RivasMario/SKYWAY-96/Case/96% Case (RobotDoctor)/Images/96plate_angle_left.png

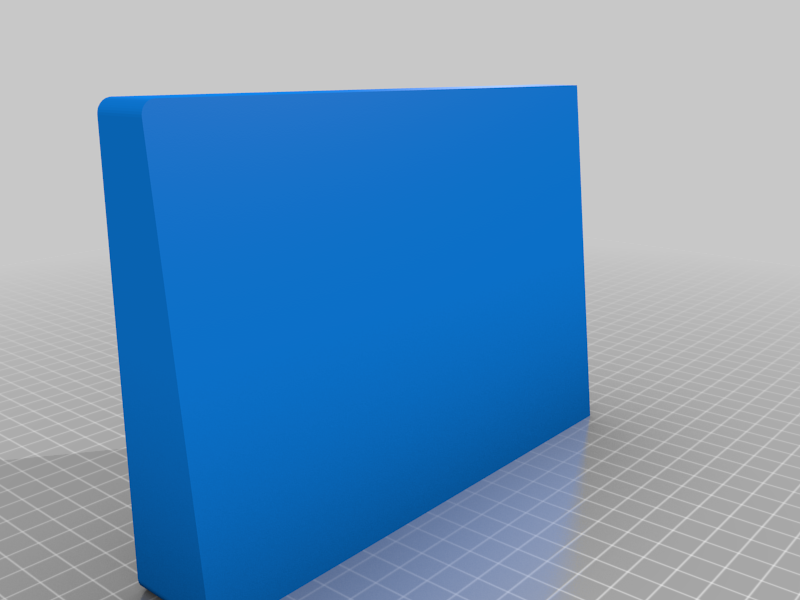
Case/96% Case (RobotDoctor)/Images/96plate_angle_left.png
