RivasMario/SKYWAY-96/Case/SKYWAY Custom (CadQuery)/output/foot_dovetail.png

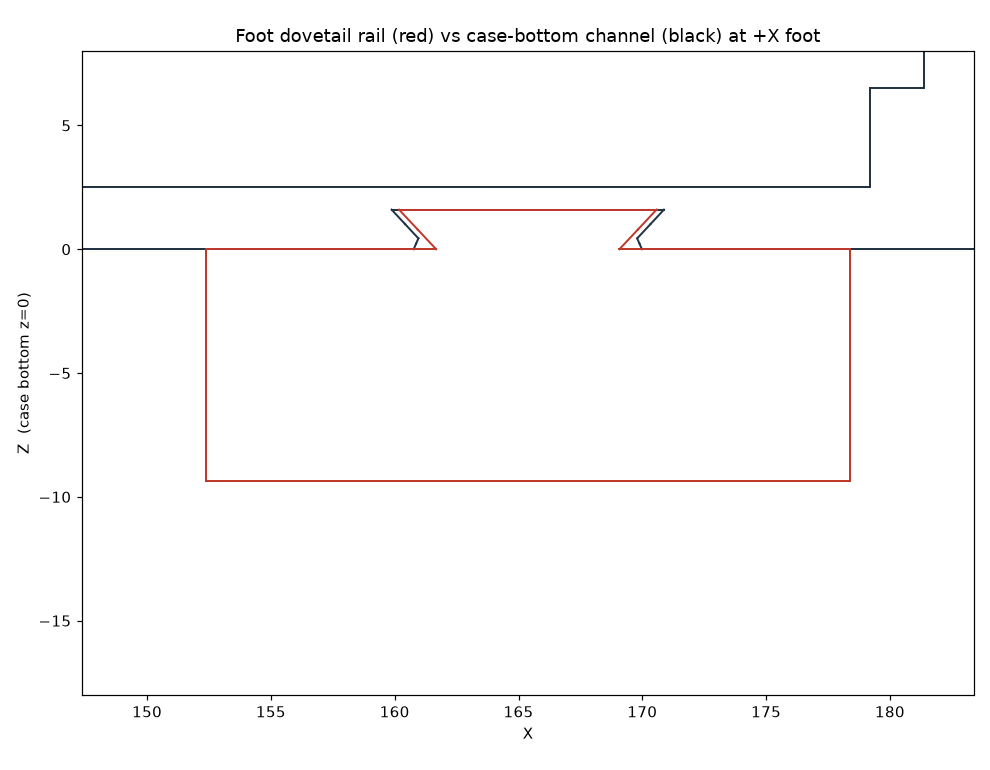
Case/SKYWAY Custom (CadQuery)/output/foot_dovetail.png
