RivasMario/SKYWAY-96/Case/SKYWAY Custom (CadQuery)/output/orientation_check.png

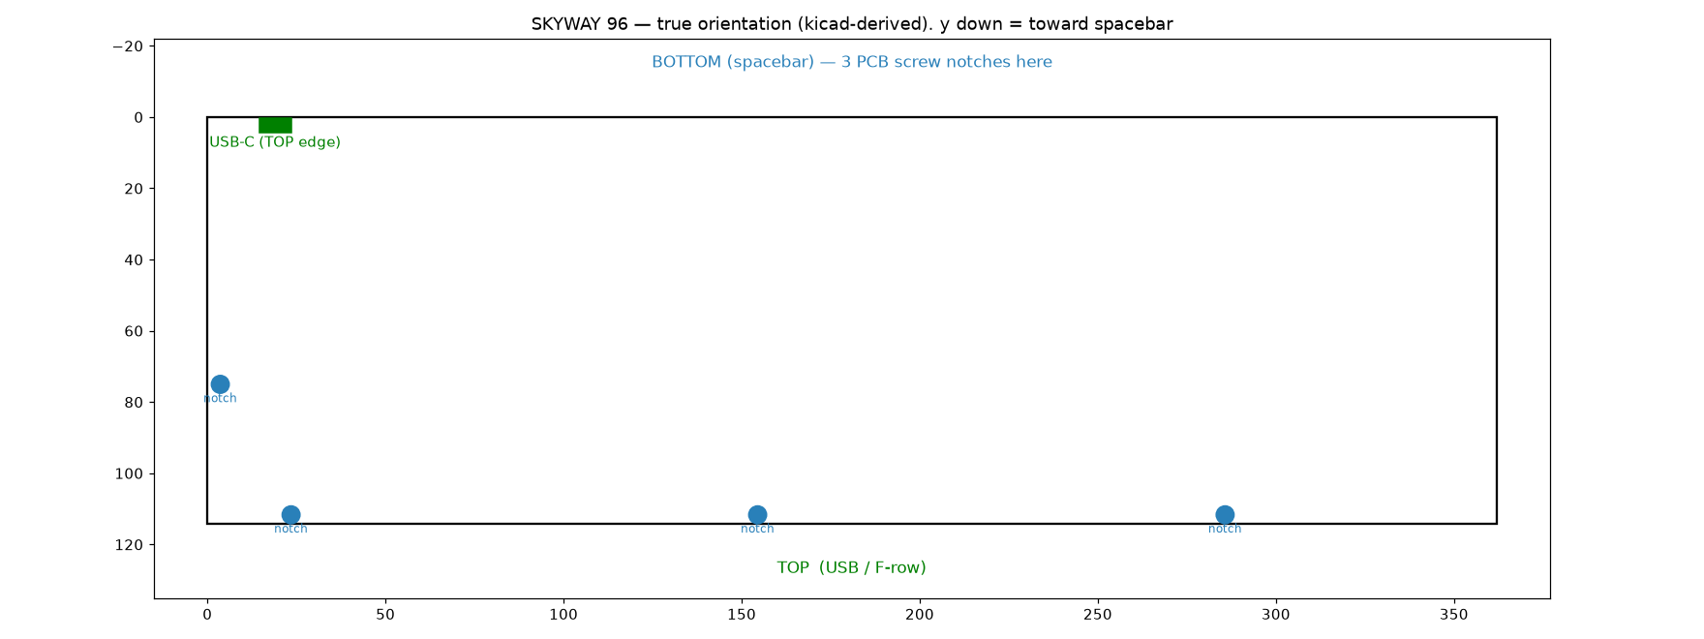
Case/SKYWAY Custom (CadQuery)/output/orientation_check.png
