RivasMario/SKYWAY-96/Case/SKYWAY Custom (CadQuery)/output/overhang_map.png

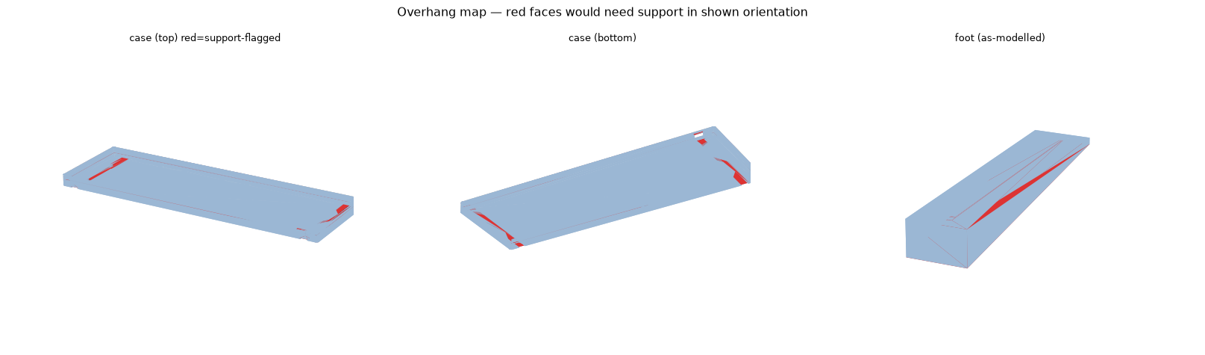
Case/SKYWAY Custom (CadQuery)/output/overhang_map.png
