RivasMario/SKYWAY-96/Case/SKYWAY Custom (CadQuery)/output/posts_topcheck.png

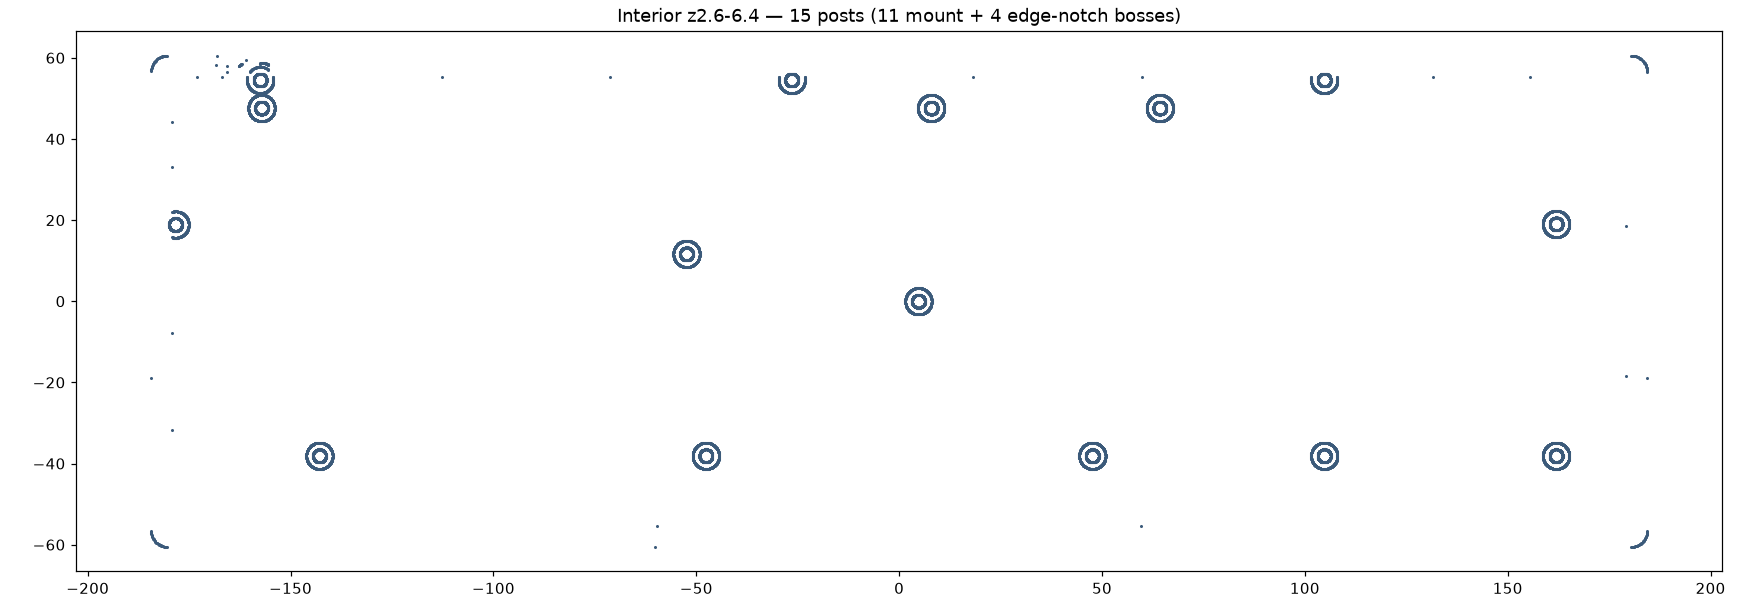
Case/SKYWAY Custom (CadQuery)/output/posts_topcheck.png
