RivasMario/SKYWAY-96/Case/SKYWAY Custom (CadQuery)/output/screw_map.png

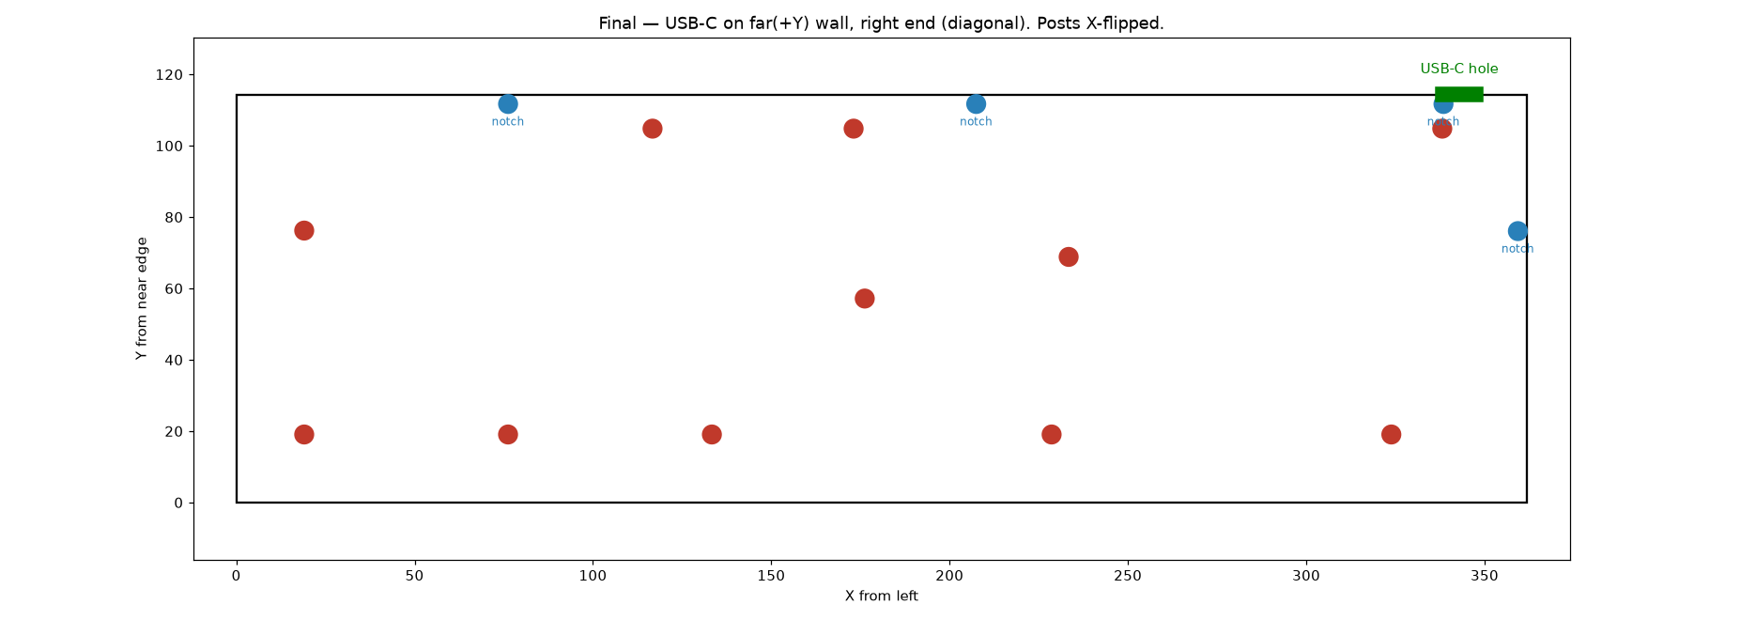
Case/SKYWAY Custom (CadQuery)/output/screw_map.png
