RivasMario/SKYWAY-96/Case/SKYWAY Custom (CadQuery)/output/split_dovetail.png

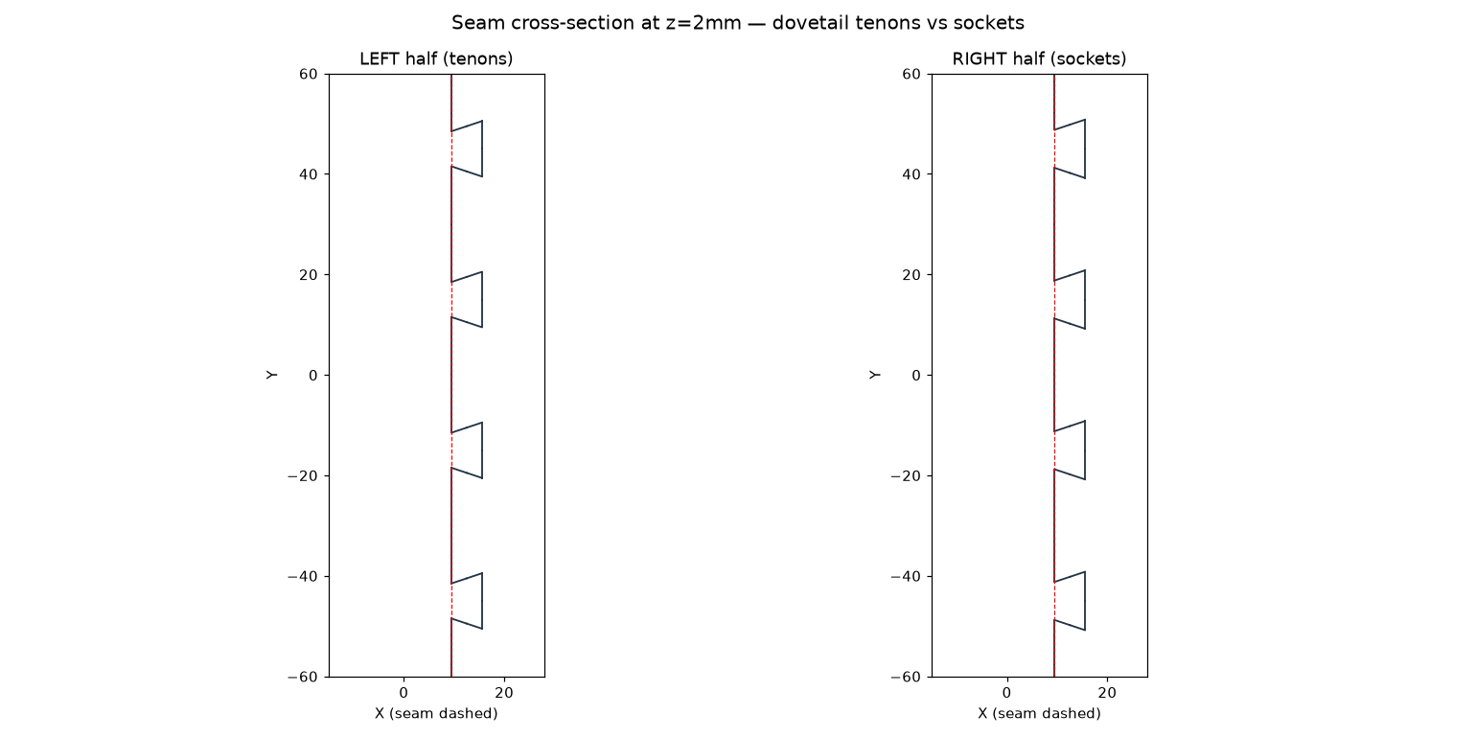
Case/SKYWAY Custom (CadQuery)/output/split_dovetail.png
