RivasMario/SKYWAY-96/Case/SKYWAY Custom (CadQuery)/output/variants_preview.png

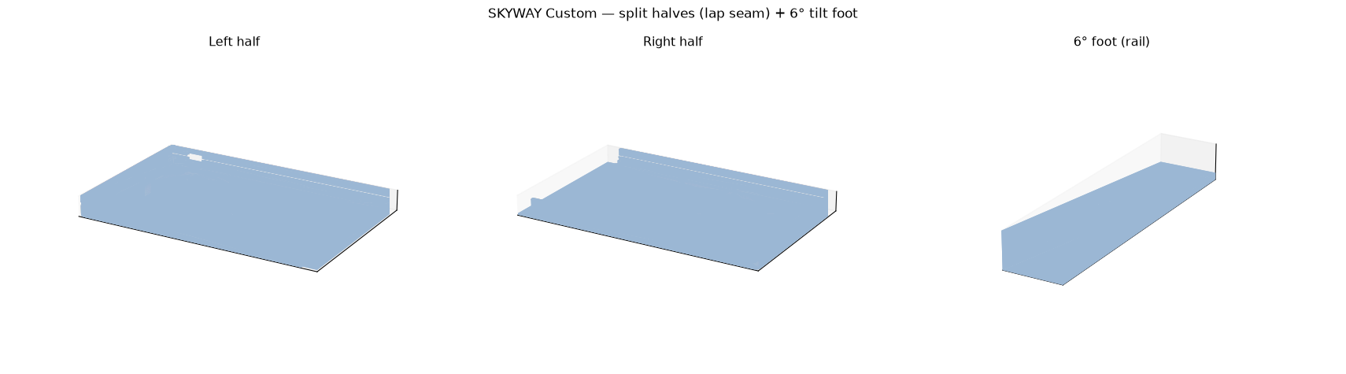
Case/SKYWAY Custom (CadQuery)/output/variants_preview.png
