RivasMario/SKYWAY-96/KLE DATA/Keys.png

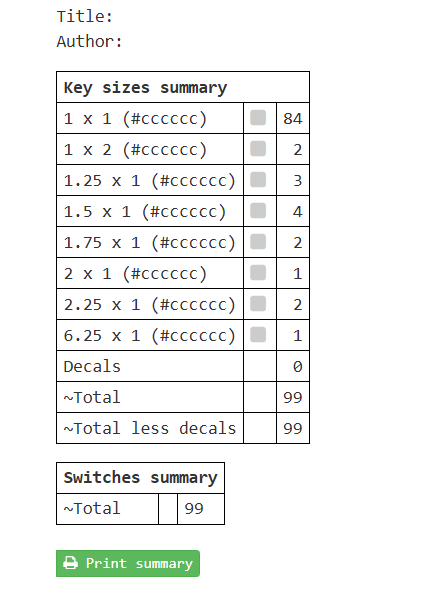
KLE DATA/Keys.png
