RivasMario/SKYWAY-96/KLE DATA/Via Labelling.png

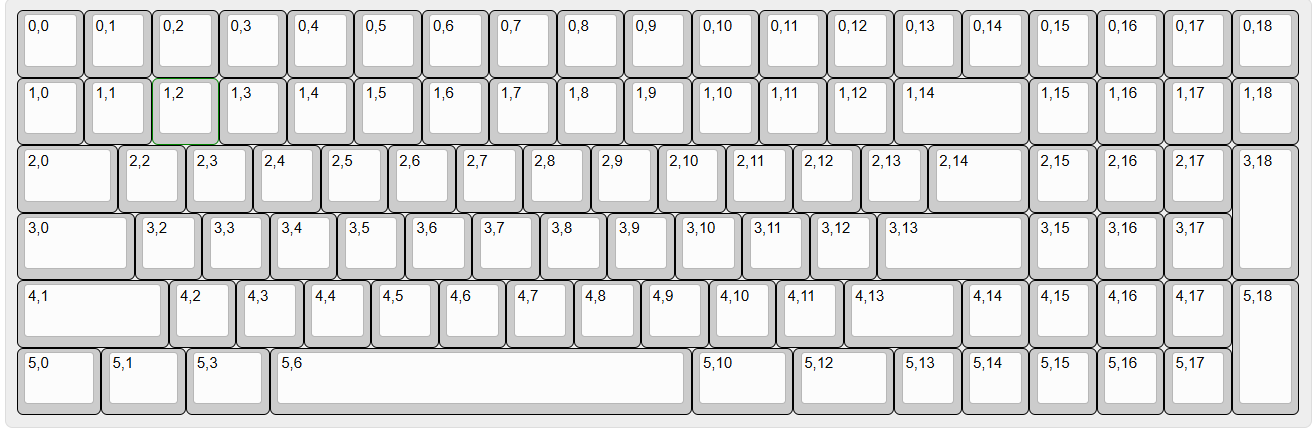
KLE DATA/Via Labelling.png
