RivasMario/SKYWAY-96/Photos/3D.webp

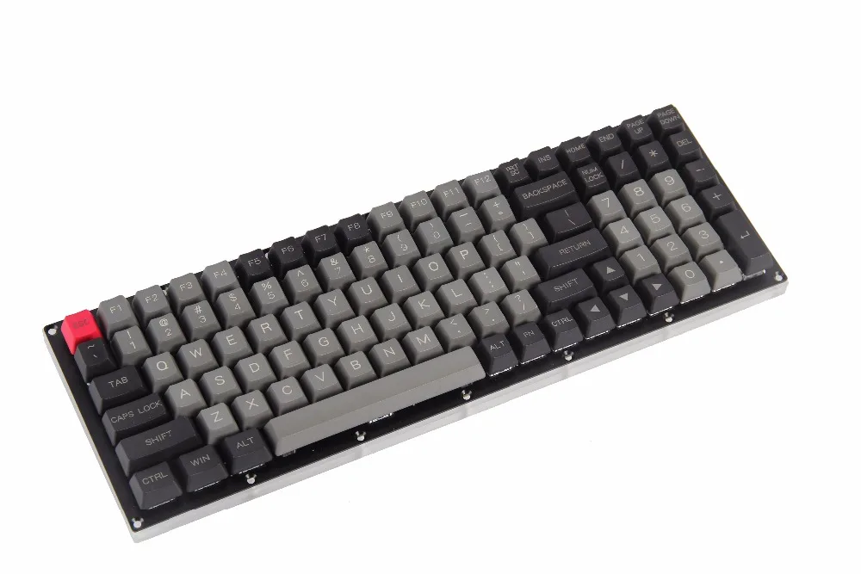
Photos/3D.webp
