RivasMario/SKYWAY-96/Photos/PCB.png

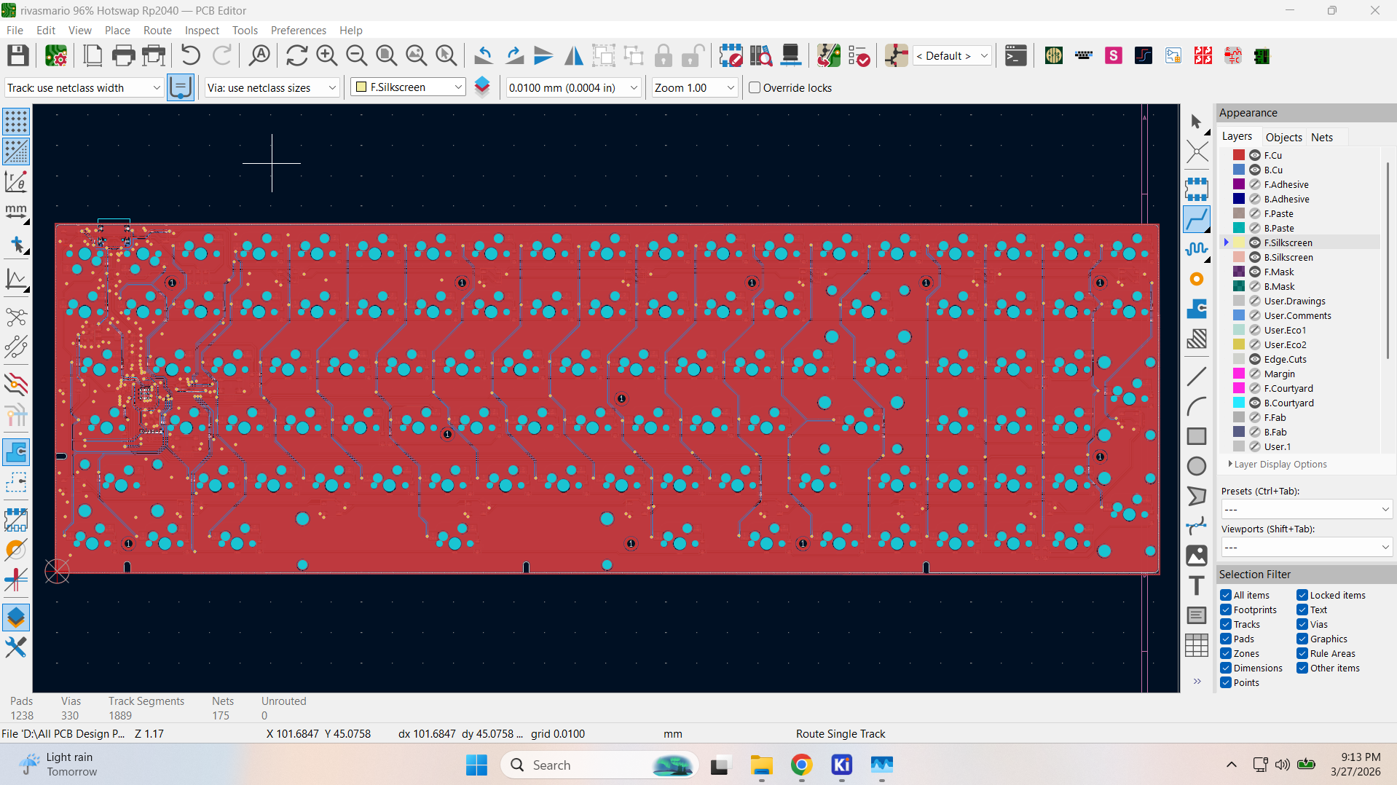
Photos/PCB.png
