RivasMario/SKYWAY-96/Photos/Stablizers.png

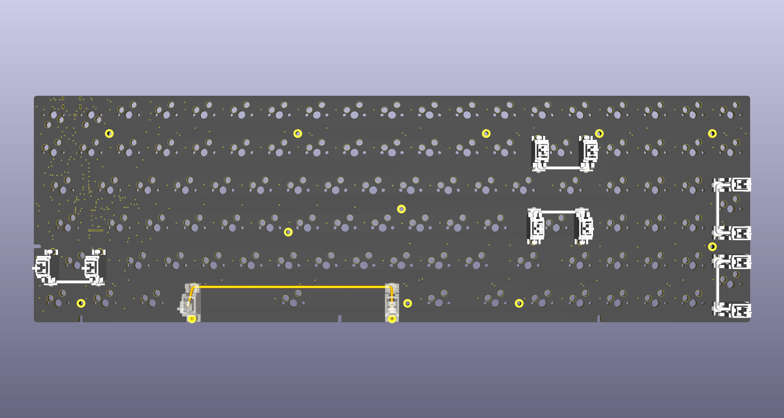
Photos/Stablizers.png
