RivasMario/SKYWAY-96/Photos/Top 2D.png

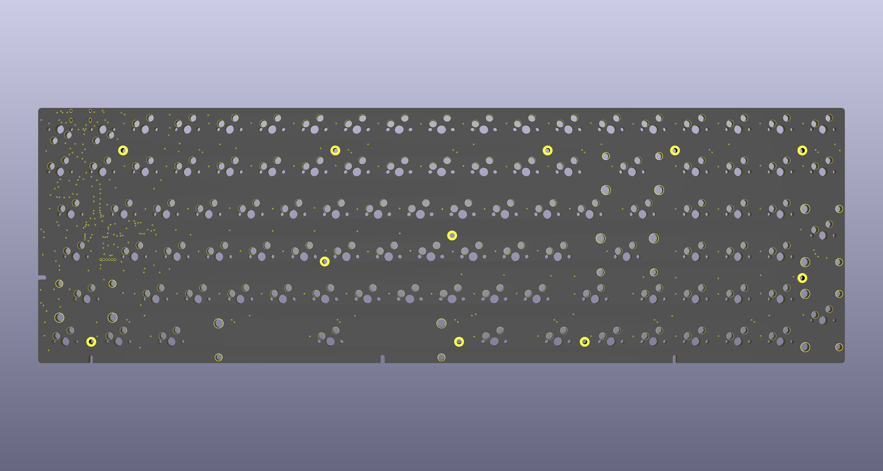
Photos/Top 2D.png
