RivasMario/SKYWAY-96/Plate (CadQuery)/output/skyway96_plate_left.preview.png

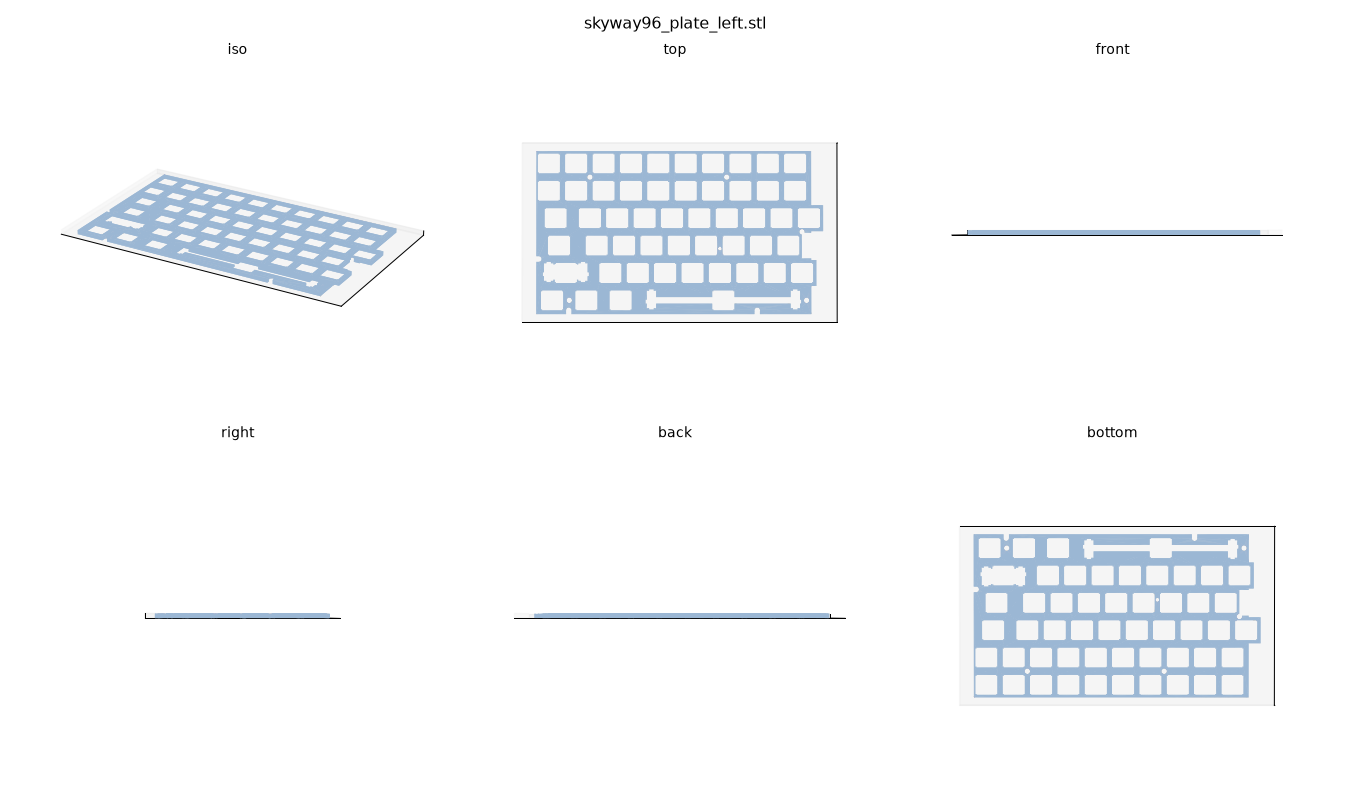
Plate (CadQuery)/output/skyway96_plate_left.preview.png
