RivasMario/SKYWAY-96/Plate (CadQuery)/output/skyway96_plate_right.stl

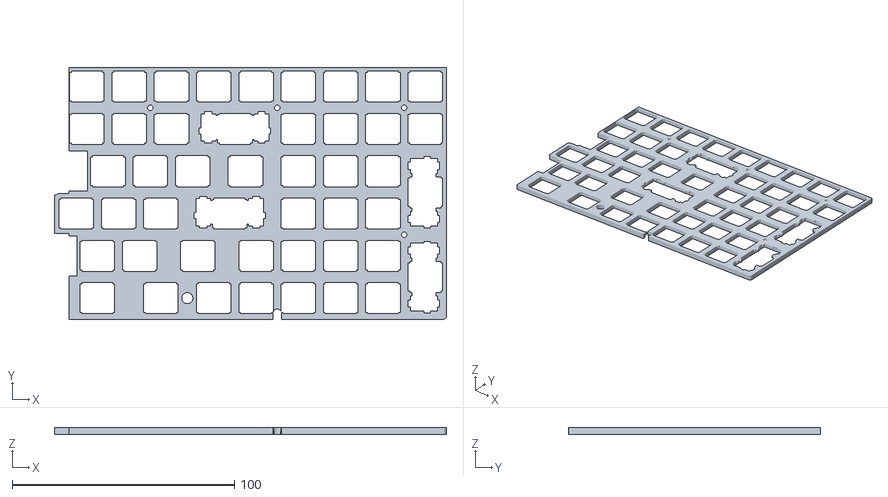
[picture p51: CAD file, 2026-06-19]
Plate (CadQuery)/output/skyway96_plate_right.stl
176.5 x 113.3 x 3.00
