RivasMario/SKYWAY-96/Case/Melody96 Case (HughMann)/Hardware/Feet.stl

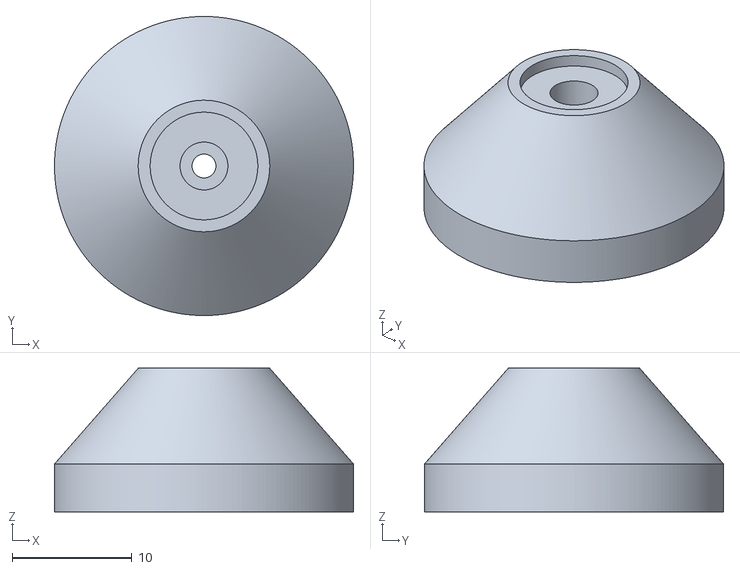
[picture p52: CAD file, 2026-06-11]
Case/Melody96 Case (HughMann)/Hardware/Feet.stl
25.0 x 25.0 x 12.0
