RivasMario/SKYWAY-96/Case/Melody96 Case (HughMann)/Main Body/Body R 2mm.stl

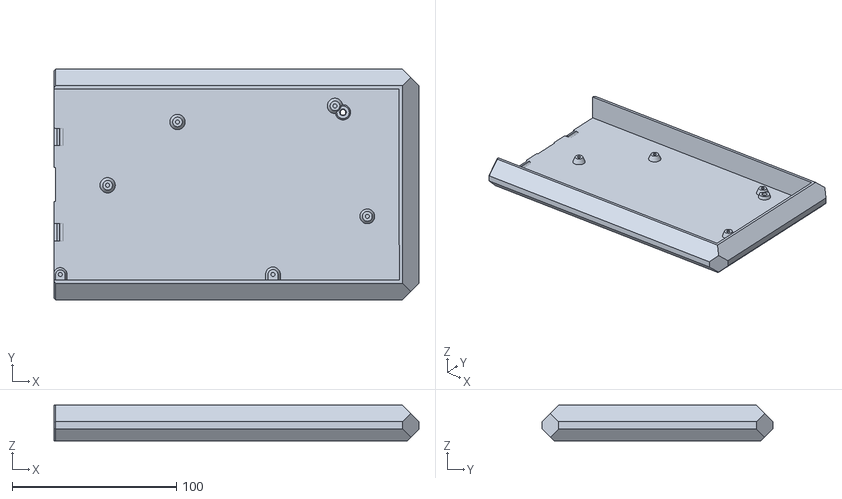
[picture p53: CAD file, 2026-06-11]
Case/Melody96 Case (HughMann)/Main Body/Body R 2mm.stl
221.9 x 140.3 x 21.7
