RivasMario/SKYWAY-96/Case/Melody96 Case (HughMann)/Remixes/Granular Theory (Stoic Reluctance) Stripe M2.stl

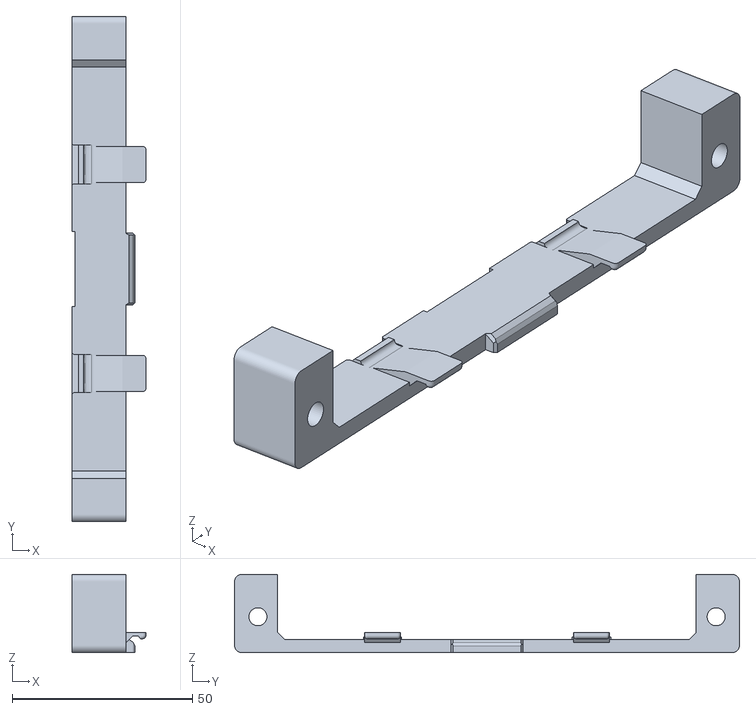
[picture p54: CAD file, 2026-06-11]
Case/Melody96 Case (HughMann)/Remixes/Granular Theory (Stoic Reluctance) Stripe M2.stl
20.5 x 140.2 x 21.7
