RivasMario/SKYWAY-96/Case/Melody96 Case (HughMann)/Risers/5 Degree Riser Single Piece.stl

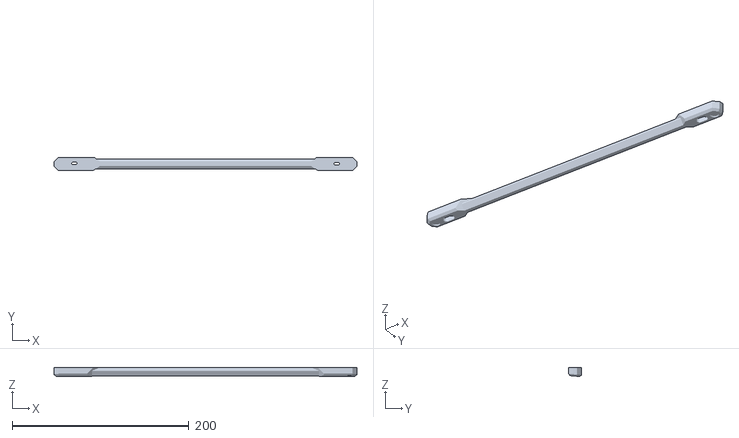
[picture p55: CAD file, 2026-06-11]
Case/Melody96 Case (HughMann)/Risers/5 Degree Riser Single Piece.stl
342.5 x 15.0 x 10.2
