RivasMario/SKYWAY-96/Case/SKYWAY Custom (CadQuery)/output/skyway96_foot.stl

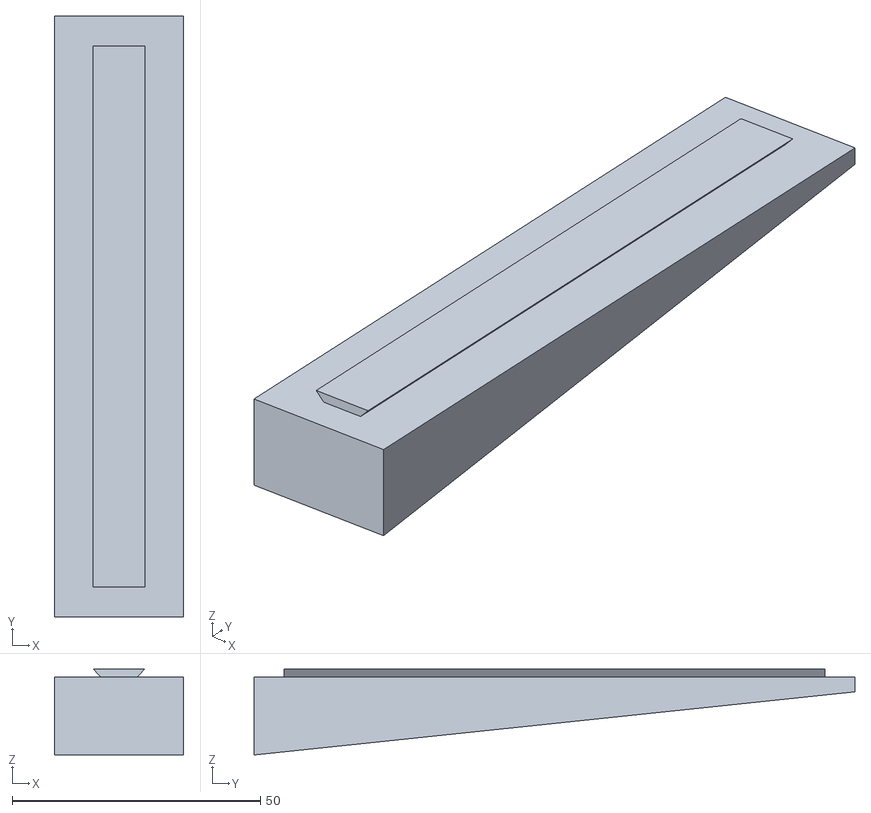
[picture p56: CAD file, 2026-06-19]
Case/SKYWAY Custom (CadQuery)/output/skyway96_foot.stl
26.0 x 121.1 x 17.3
