RivasMario/SKYWAY-96/Plate (CadQuery)/output/skyway96_plate_left.stl

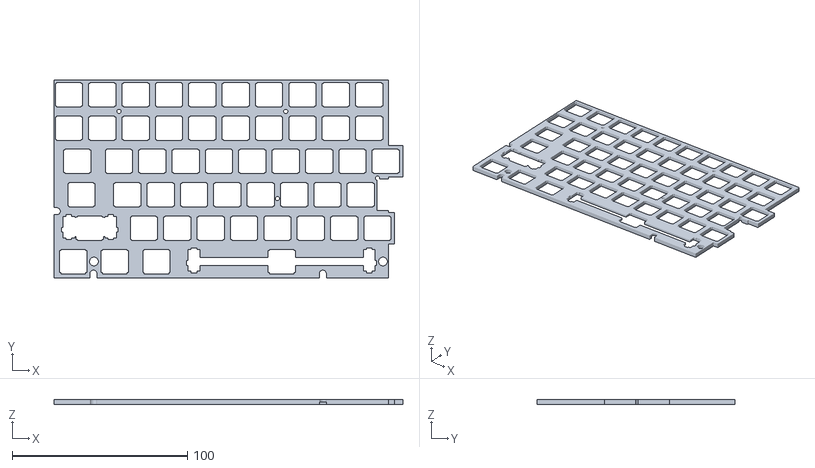
[picture p57: CAD file, 2026-06-19]
Plate (CadQuery)/output/skyway96_plate_left.stl
199.3 x 113.3 x 3.00
