RivasMario/SKYWAY-96/Case/96% Case (RobotDoctor)/Main Body/96plate_flat_left.STL

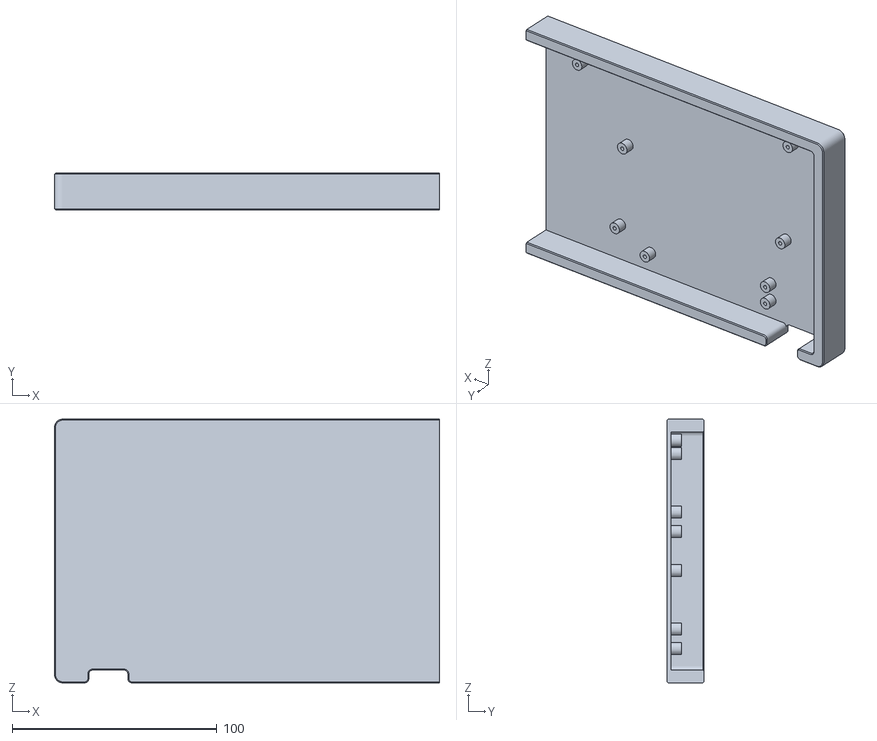
[picture p58: CAD file, 2026-06-11]
Case/96% Case (RobotDoctor)/Main Body/96plate_flat_left.STL
188.0 x 18.0 x 128.8
