RivasMario/SKYWAY-96/Case/Melody96 Case (HughMann)/Main Body/Body R.stl

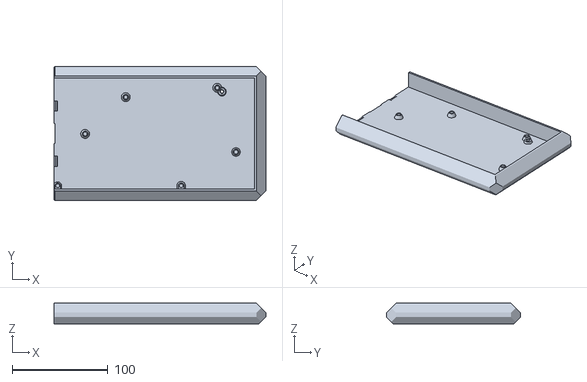
[picture p59: CAD file, 2026-06-11]
Case/Melody96 Case (HughMann)/Main Body/Body R.stl
221.9 x 140.3 x 21.7
