RivasMario/SKYWAY-96/Case/Melody96 Case (HughMann)/Remixes/Granular Theory (Stoic Reluctance) Body R M2.stl

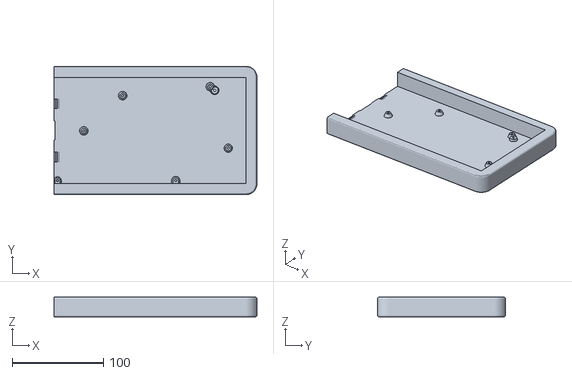
[picture p60: CAD file, 2026-06-11]
Case/Melody96 Case (HughMann)/Remixes/Granular Theory (Stoic Reluctance) Body R M2.stl
221.9 x 140.2 x 21.7
