RivasMario/SKYWAY-96/Case/SKYWAY Custom (CadQuery)/output/skyway96_left.stl

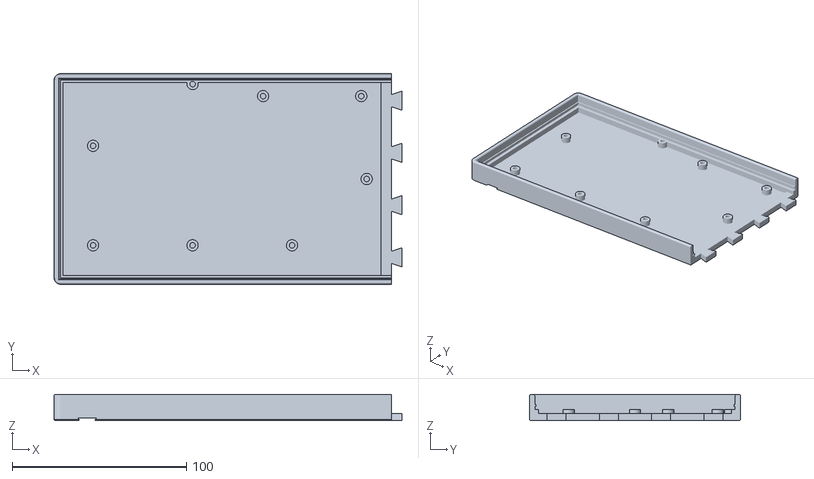
[picture p61: CAD file, 2026-06-19]
Case/SKYWAY Custom (CadQuery)/output/skyway96_left.stl
199.9 x 121.1 x 15.1
