RivasMario/SKYWAY-96/Case/Melody96 Case (HughMann)/Main Body/Stripe.stl

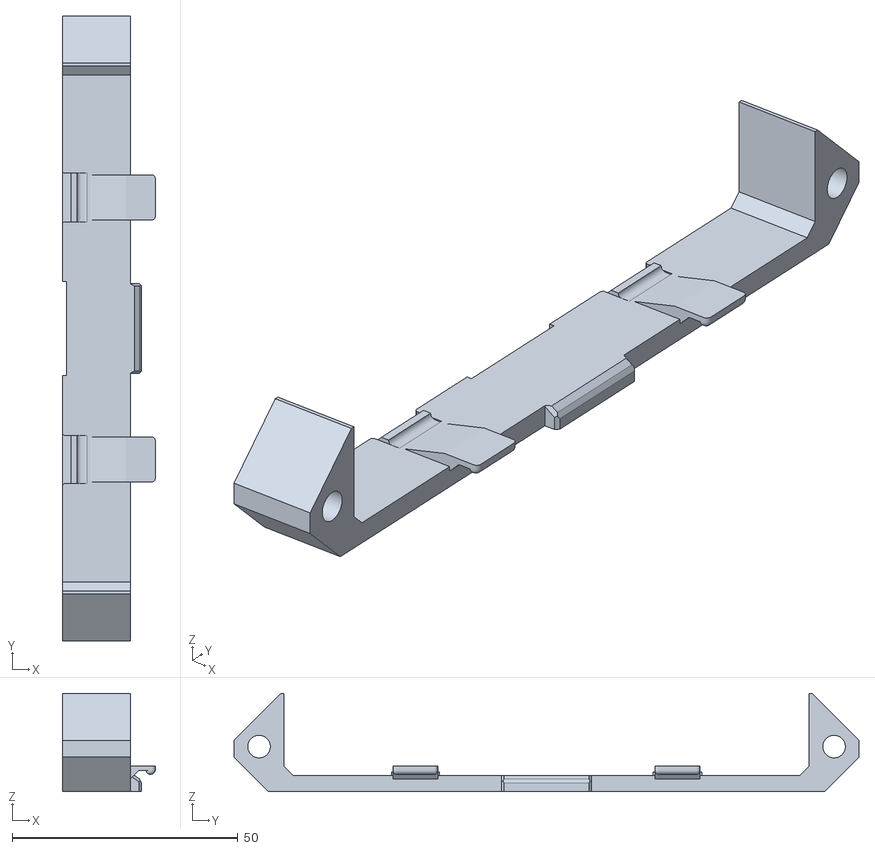
[picture p62: CAD file, 2026-06-11]
Case/Melody96 Case (HughMann)/Main Body/Stripe.stl
20.5 x 138.3 x 21.7
