RivasMario/SKYWAY-96/KLE DATA/Wiring.png

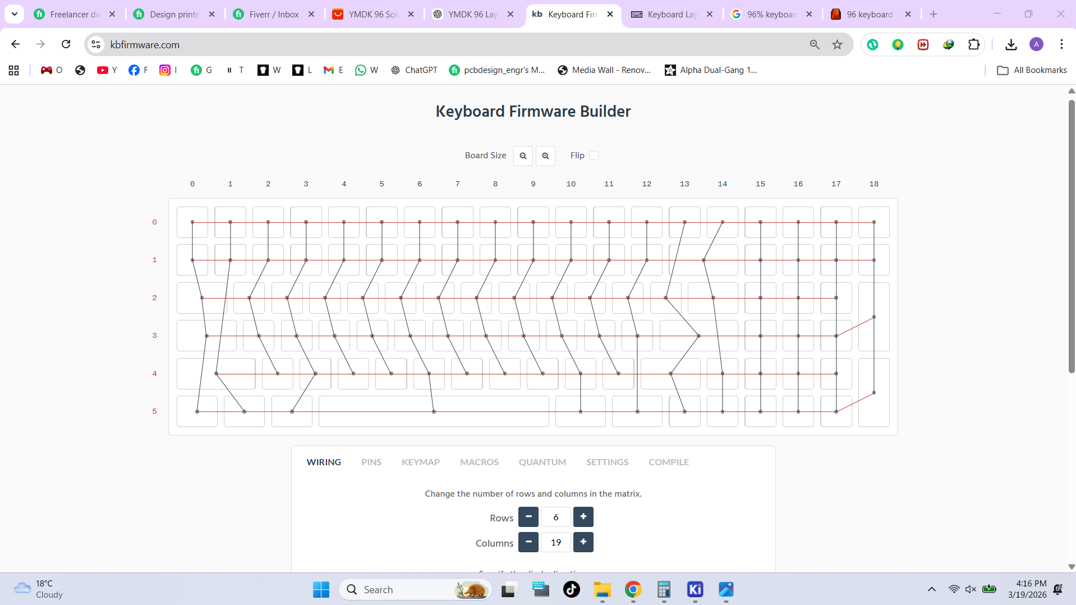
KLE DATA/Wiring.png
