RivasMario/SKYWAY-96/KiCAD Source Files/RGBLeds.kicad_sch

## KiCad design KiCAD Source Files/RGBLeds.kicad_sch (2026-05-01)

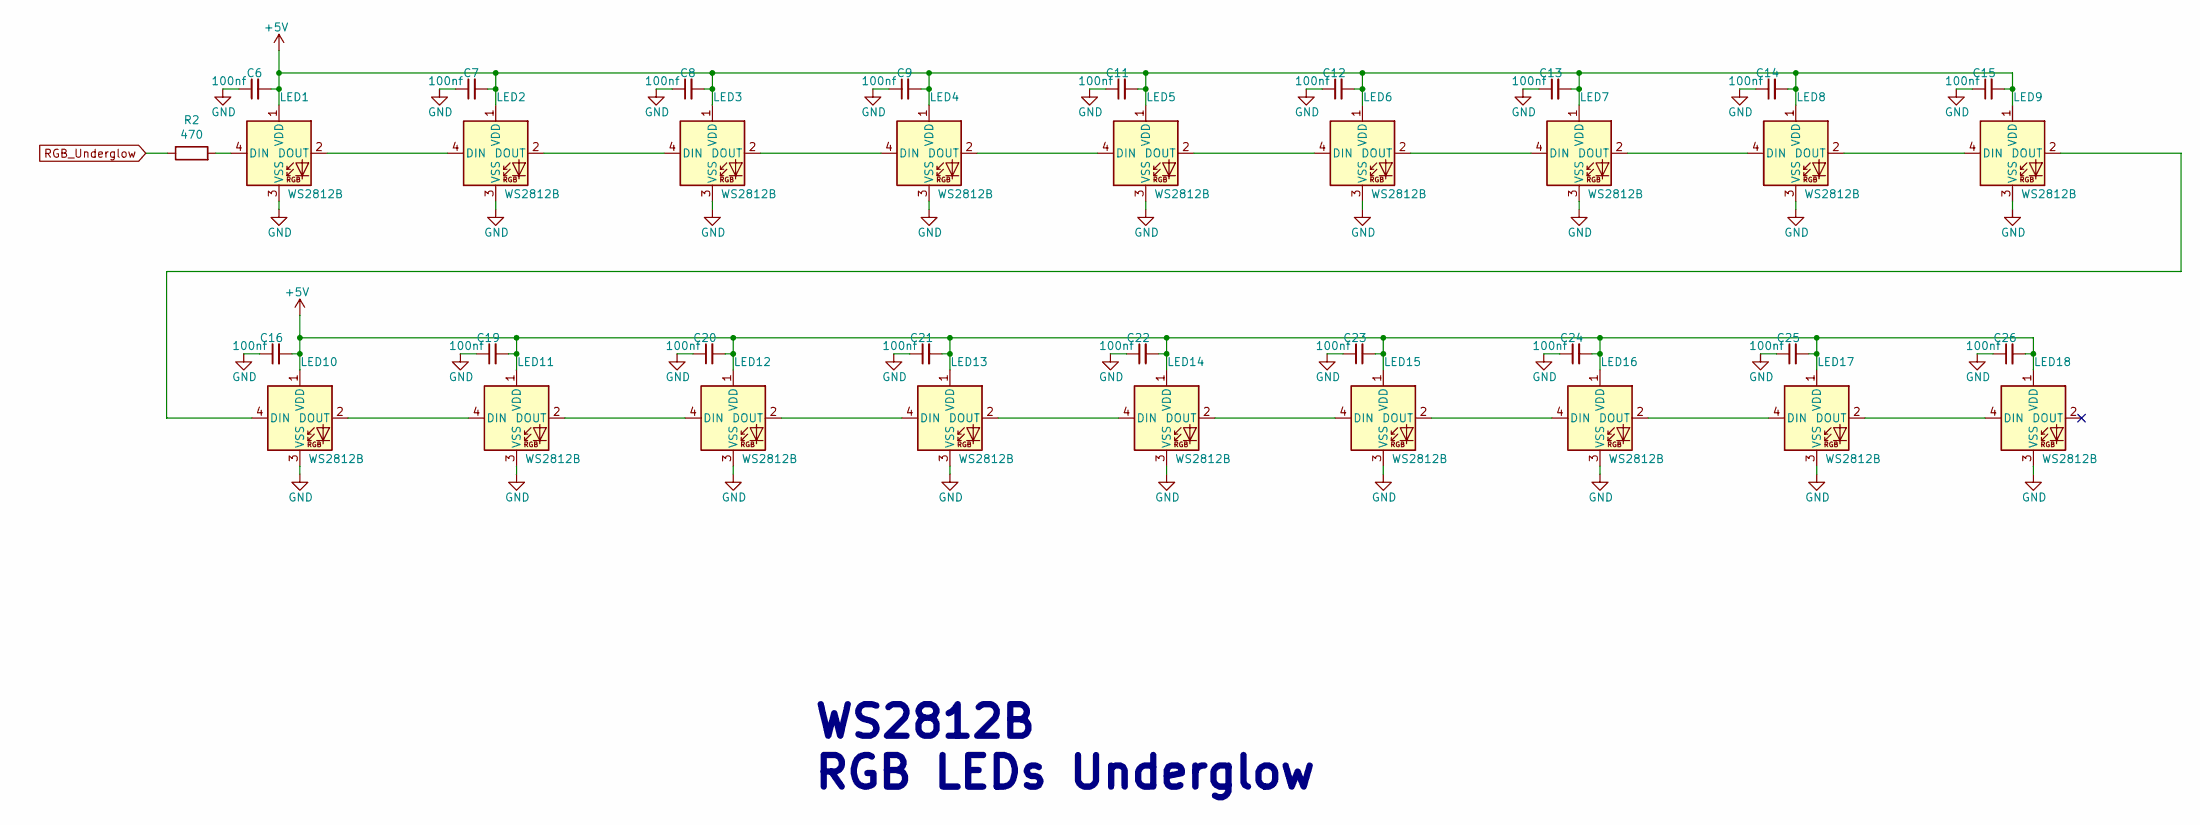
[picture p77: schematic RGBLeds.kicad_sch]

Parts:
C6, C7, C8, C9, C11, C12, C13, C14, C15, C16, C19, C20, C21, C22, C23, C24, C25, C26: 100nf; JLCPCB_C0402; JLCPCB Part # C77020
LED1, LED2, LED3, LED4, LED5, LED6, LED7, LED8, LED9, LED10, LED11, LED12, LED13, LED14, LED15, LED16, LED17, LED18: WS2812B; LED_WS2812B_PLCC4_5.0x5.0mm_P3.2mm; JLCPCB Part # C2761795
R2: 470; JLCPCB_R0402; JLCPCB Part # C25117

Connections:
+5V: C6.2, C7.2, C8.2, C9.2, C11.2, C12.2, C13.2, C14.2, C15.2, C16.2, C19.2, C20.2, C21.2, C22.2, C23.2, C24.2, C25.2, C26.2, LED1.1 (VDD), LED2.1 (VDD), LED3.1 (VDD), LED4.1 (VDD), LED5.1 (VDD), LED6.1 (VDD), LED7.1 (VDD), LED8.1 (VDD), LED9.1 (VDD), LED10.1 (VDD), LED11.1 (VDD), LED12.1 (VDD), LED13.1 (VDD), LED14.1 (VDD), LED15.1 (VDD), LED16.1 (VDD), LED17.1 (VDD), LED18.1 (VDD)
GND: C6.1, C7.1, C8.1, C9.1, C11.1, C12.1, C13.1, C14.1, C15.1, C16.1, C19.1, C20.1, C21.1, C22.1, C23.1, C24.1, C25.1, C26.1, LED1.3 (VSS), LED2.3 (VSS), LED3.3 (VSS), LED4.3 (VSS), LED5.3 (VSS), LED6.3 (VSS), LED7.3 (VSS), LED8.3 (VSS), LED9.3 (VSS), LED10.3 (VSS), LED11.3 (VSS), LED12.3 (VSS), LED13.3 (VSS), LED14.3 (VSS), LED15.3 (VSS), LED16.3 (VSS), LED17.3 (VSS), LED18.3 (VSS)
unnamed: LED1.2 (DOUT), LED2.4 (DIN)
unnamed: LED1.4 (DIN), R2.2
unnamed: LED2.2 (DOUT), LED3.4 (DIN)
unnamed: LED3.2 (DOUT), LED4.4 (DIN)
unnamed: LED4.2 (DOUT), LED5.4 (DIN)
unnamed: LED5.2 (DOUT), LED6.4 (DIN)
unnamed: LED6.2 (DOUT), LED7.4 (DIN)
unnamed: LED7.2 (DOUT), LED8.4 (DIN)
unnamed: LED8.2 (DOUT), LED9.4 (DIN)
unnamed: LED10.2 (DOUT), LED11.4 (DIN)
unnamed: LED9.2 (DOUT), LED10.4 (DIN)
unnamed: LED11.2 (DOUT), LED12.4 (DIN)
unnamed: LED12.2 (DOUT), LED13.4 (DIN)
unnamed: LED13.2 (DOUT), LED14.4 (DIN)
unnamed: LED14.2 (DOUT), LED15.4 (DIN)
unnamed: LED15.2 (DOUT), LED16.4 (DIN)
unnamed: LED16.2 (DOUT), LED17.4 (DIN)
unnamed: LED17.2 (DOUT), LED18.4 (DIN)
RGB_Underglow: R2.1

Notes on the sheet:
WS2812B RGB LEDs Underglow
