RivasMario/SKYWAY-96/KiCAD Source Files/rivasmario 96% Hotswap Rp2040.kicad_sch

## KiCad design KiCAD Source Files/rivasmario 96% Hotswap Rp2040.kicad_sch (2026-05-01)

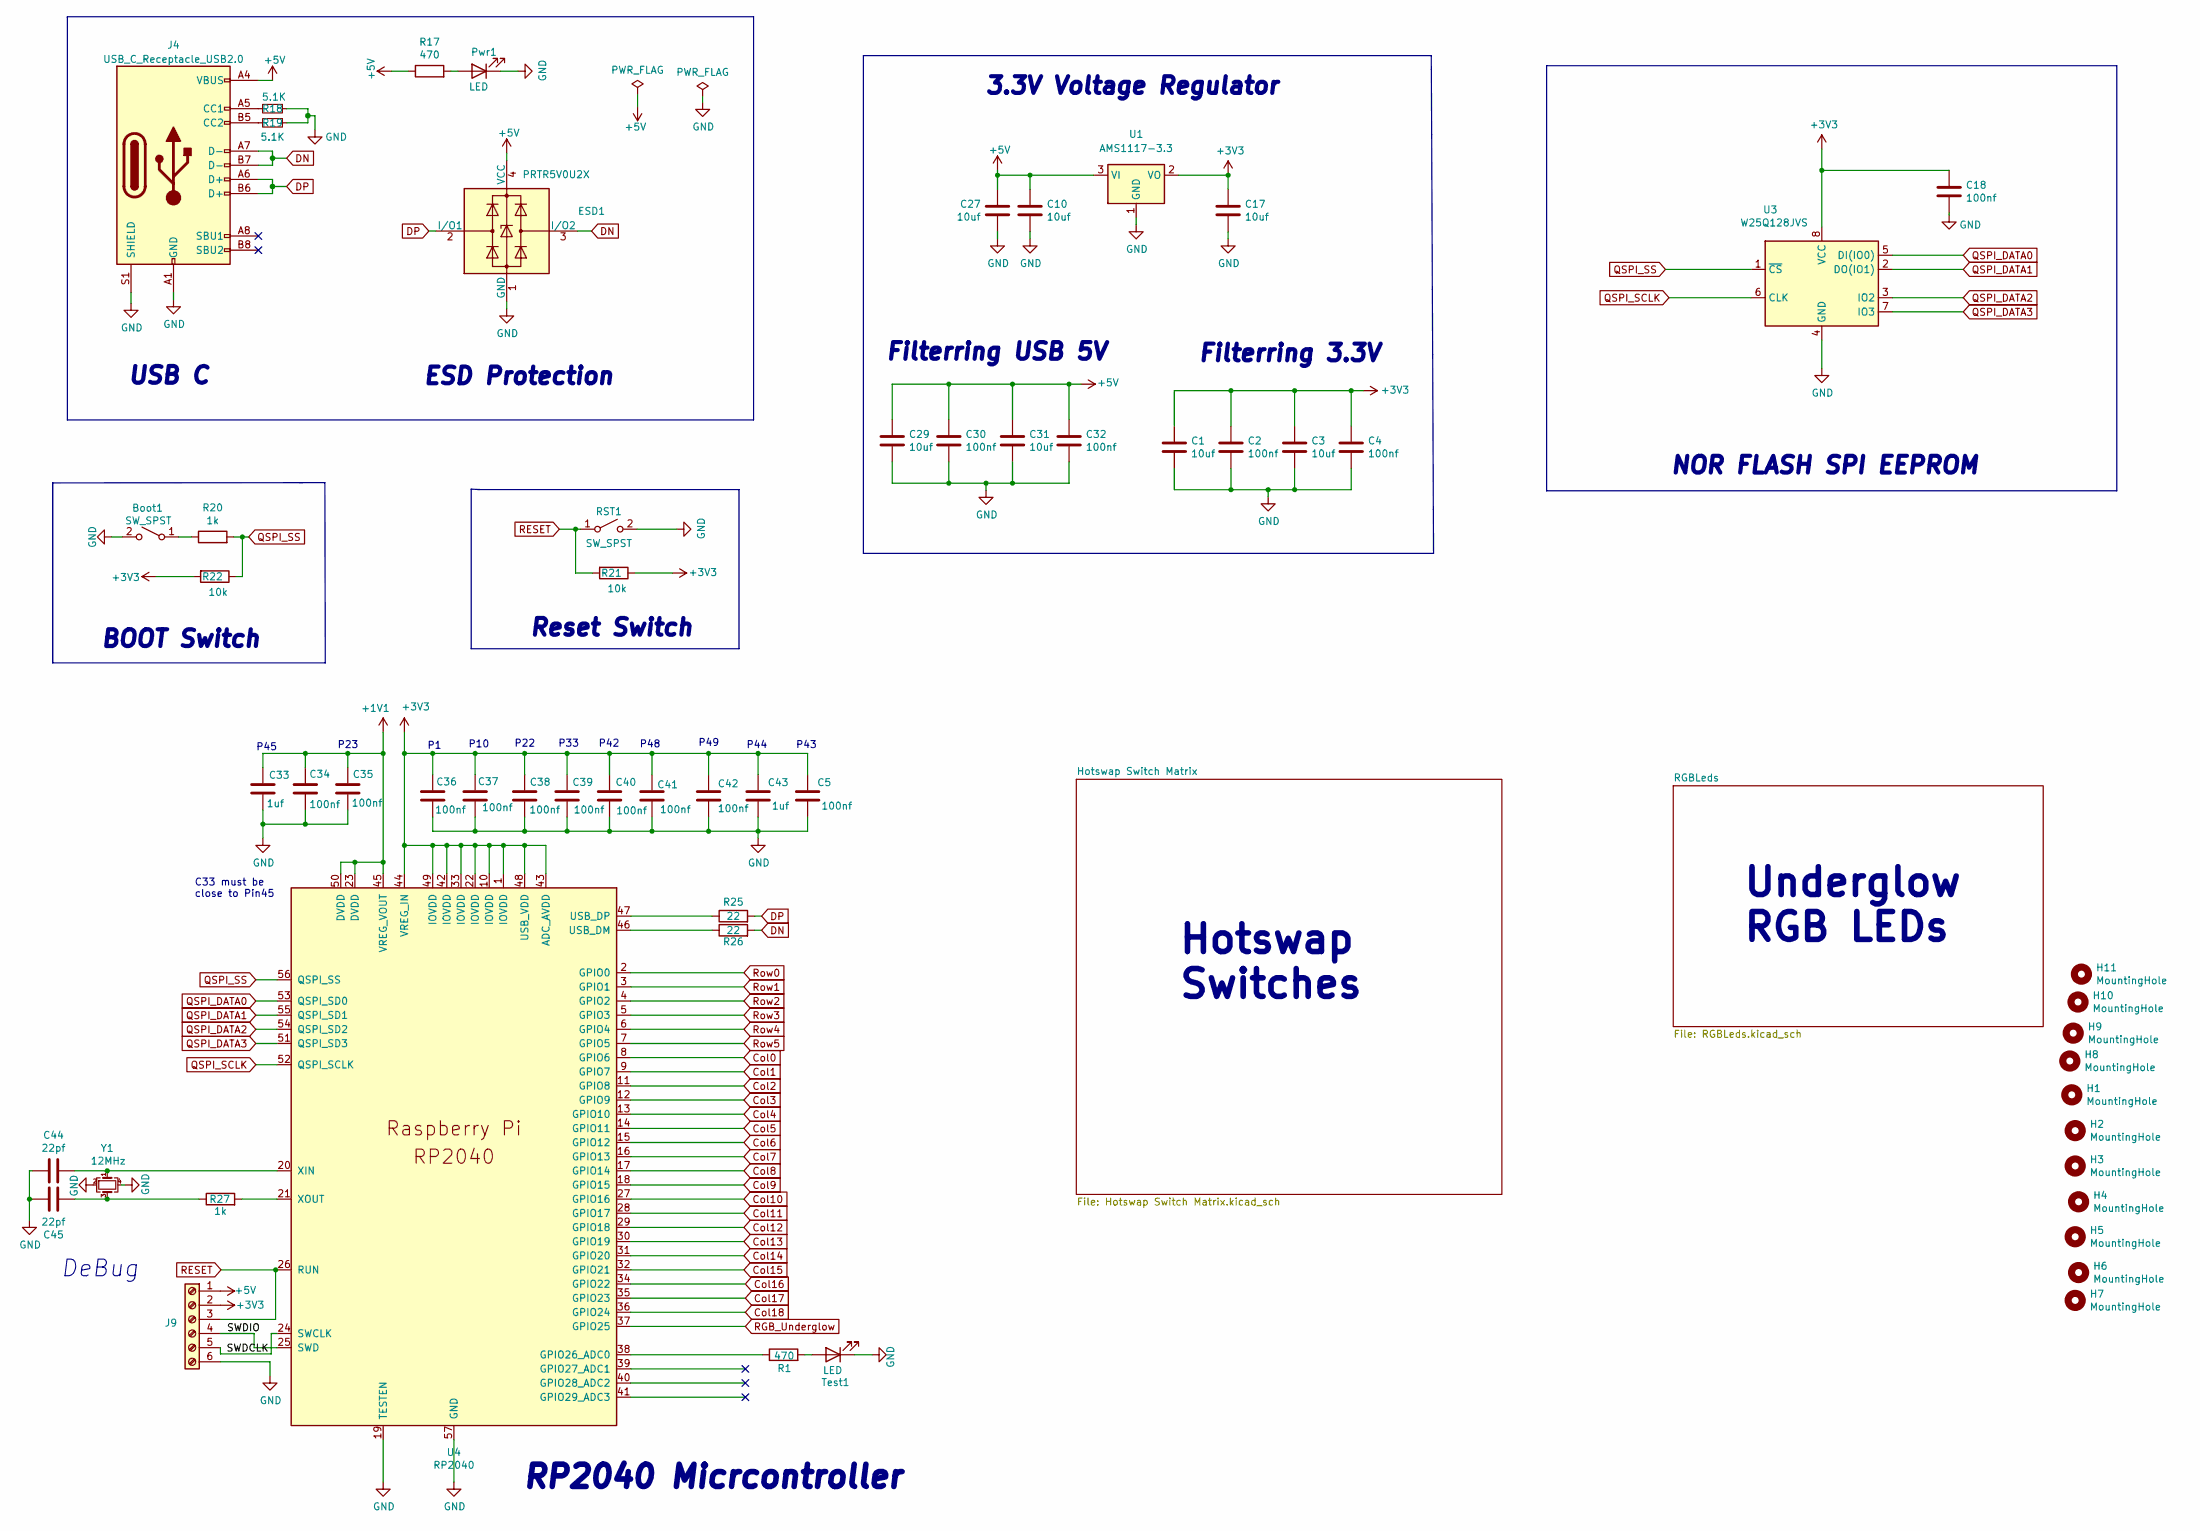
[picture p78: schematic rivasmario 96% Hotswap Rp2040.kicad_sch]

Parts:
Boot1: SW_SPST; K2-1187SQ-A4SW-06; JLCPCB Part # C92584
C1, C3, C10, C17, C27, C29, C31: 10uf; C_0805_2012Metric; JLCPCB Part # C440198
C2, C4, C30, C32: 100nf; C_0805_2012Metric; JLCPCB Part # C126469
C5, C18, C34, C35, C36, C37, C38, C39, C40, C41, C42: 100nf; JLCPCB_C0402; JLCPCB Part # C77020
C33, C43: 1uf; JLCPCB_C0402; JLCPCB Part # C1518208
C44, C45: 22pf; JLCPCB_C0402; JLCPCB Part # C1555
ESD1: PRTR5V0U2X; JLCPCB Part # C2827688
H1, H2, H3, H4, H5, H6, H7, H8, H9, H10, H11: MountingHole; MountingHole_2.2mm_M2_Pad
J4: USB_C_Receptacle_USB2.0; USB_C_Receptacle_HRO_TYPE-C-31-M-12; JLCPCB Part # C165948
J9: Screw_Terminal_01x06; PinHeader_1x06_P1.27mm_Vertical
Pwr1: LED; LED_0402_1005Metric; JLCPCB Part # C131223
R1, R17: 470; JLCPCB_R0402; JLCPCB Part # C25117
R18, R19: 5.1K; JLCPCB_R0402; JLCPCB Part # C25905
R20, R27: 1k; JLCPCB_R0402; JLCPCB Part # C11702
R21, R22: 10k; JLCPCB_R0402; JLCPCB Part # C25744
R25, R26: 22; JLCPCB_R0402; JLCPCB Part # C25092
RST1: SW_SPST; K2-1187SQ-A4SW-06; JLCPCB Part # C92584
Test1: LED; LED_0402_1005Metric; JLCPCB Part # C131223
U1: AMS1117-3.3; SOT-223-3_TabPin2; JLCPCB Part # C6186
U3: W25Q128JVS; SOIC-8_5.23x5.23mm_P1.27mm; JLCPCB Part # C97521
U4: RP2040; RP2040-QFN-56; JLCPCB Part # C2040
Y1: 12MHz; Crystal_SMD_3225-4Pin_3.2x2.5mm; JLCPCB Part # C9002

Connections:
+1V1: C33.1, C34.1, C35.1, U4.23 (DVDD), U4.45 (VREG_VOUT), U4.50 (DVDD)
+3V3: C1.1, C2.1, C3.1, C4.1, C5.1, C17.1, C18.1, C36.1, C37.1, C38.1, C39.1, C40.1, C41.1, C42.1, C43.1, J9.2, R21.1, R22.2, U1.2 (VO), U3.8 (VCC), U4.1 (IOVDD), U4.10 (IOVDD), U4.22 (IOVDD), U4.33 (IOVDD), U4.42 (IOVDD), U4.43 (ADC_AVDD), U4.44 (VREG_IN), U4.48 (USB_VDD), U4.49 (IOVDD)
+5V: C10.1, C27.1, C29.1, C30.1, C31.1, C32.1, ESD1.4 (VCC), J4.A4 (VBUS), J4.A9 (VBUS), J4.B4 (VBUS), J4.B9 (VBUS), J9.1, R17.1, U1.3 (VI)
Col0: U4.8 (GPIO6)
Col1: U4.9 (GPIO7)
Col2: U4.11 (GPIO8)
Col3: U4.12 (GPIO9)
Col4: U4.13 (GPIO10)
Col5: U4.14 (GPIO11)
Col6: U4.15 (GPIO12)
Col7: U4.16 (GPIO13)
Col8: U4.17 (GPIO14)
Col9: U4.18 (GPIO15)
Col10: U4.27 (GPIO16)
Col11: U4.28 (GPIO17)
Col12: U4.29 (GPIO18)
Col13: U4.30 (GPIO19)
Col14: U4.31 (GPIO20)
Col15: U4.32 (GPIO21)
Col16: U4.34 (GPIO22)
Col17: U4.35 (GPIO23)
Col18: U4.36 (GPIO24)
DN: ESD1.3 (I/O2), J4.A7 (D-), J4.B7 (D-), R26.2
DP: ESD1.2 (I/O1), J4.A6 (D+), J4.B6 (D+), R25.2
GND: Boot1.2 (B), C1.2, C2.2, C3.2, C4.2, C5.2, C10.2, C17.2, C18.2, C27.2, C29.2, C30.2, C31.2, C32.2, C33.2, C34.2, C35.2, C36.2, C37.2, C38.2, C39.2, C40.2, C41.2, C42.2, C43.2, C44.2, C45.1, ESD1.1 (GND), J4.A1 (GND), J4.A12 (GND), J4.B1 (GND), J4.B12 (GND), J4.S1 (SHIELD), J9.6, Pwr1.1 (K), R18.1, R19.1, RST1.2 (B), Test1.1 (K), U1.1 (GND), U3.4 (GND), U4.19 (TESTEN), U4.57 (GND), Y1.2, Y1.4
unnamed: Boot1.1 (A), R20.1
unnamed: C44.1, U4.20 (XIN), Y1.1
unnamed: C45.2, R27.1, Y1.3
unnamed: J4.A5 (CC1), R18.2
unnamed: J4.B5 (CC2), R19.2
unnamed: Pwr1.2 (A), R17.2
unnamed: R1.1, U4.38 (GPIO26_ADC0)
unnamed: R1.2, Test1.2 (A)
unnamed: R25.1, U4.47 (USB_DP)
unnamed: R26.1, U4.46 (USB_DM)
unnamed: R27.2, U4.21 (XOUT)
QSPI_DATA0: U3.5 (DI(IO0)), U4.53 (QSPI_SD0)
QSPI_DATA1: U3.2 (DO(IO1)), U4.55 (QSPI_SD1)
QSPI_DATA2: U3.3 (IO2), U4.54 (QSPI_SD2)
QSPI_DATA3: U3.7 (IO3), U4.51 (QSPI_SD3)
QSPI_SCLK: U3.6 (CLK), U4.52 (QSPI_SCLK)
QSPI_SS: R20.2, R22.1, U3.1 (~CS), U4.56 (QSPI_SS)
RESET: J9.3, R21.2, RST1.1 (A), U4.26 (RUN)
RGB_Underglow: U4.37 (GPIO25)
Row0: U4.2 (GPIO0)
Row1: U4.3 (GPIO1)
Row2: U4.4 (GPIO2)
Row3: U4.5 (GPIO3)
Row4: U4.6 (GPIO4)
Row5: U4.7 (GPIO5)
SWDCLK: J9.5, U4.24 (SWCLK)
SWDIO: J9.4, U4.25 (SWD)

Notes on the sheet:
DeBug
ESD Protection
C33 must be close to Pin45
P33
P42
P23
Filterring USB 5V
P45
P49
P43
P44
BOOT Switch
P10
P22
NOR FLASH SPI EEPROM
P48
3.3V Voltage Regulator
Reset Switch
RP2040 Micrcontroller
USB C
Filterring 3.3V
Hotswap Switches
Underglow RGB LEDs
